AndrewJ-25/Digisax/CAD/3D_printing/step/key_low_bflat.step

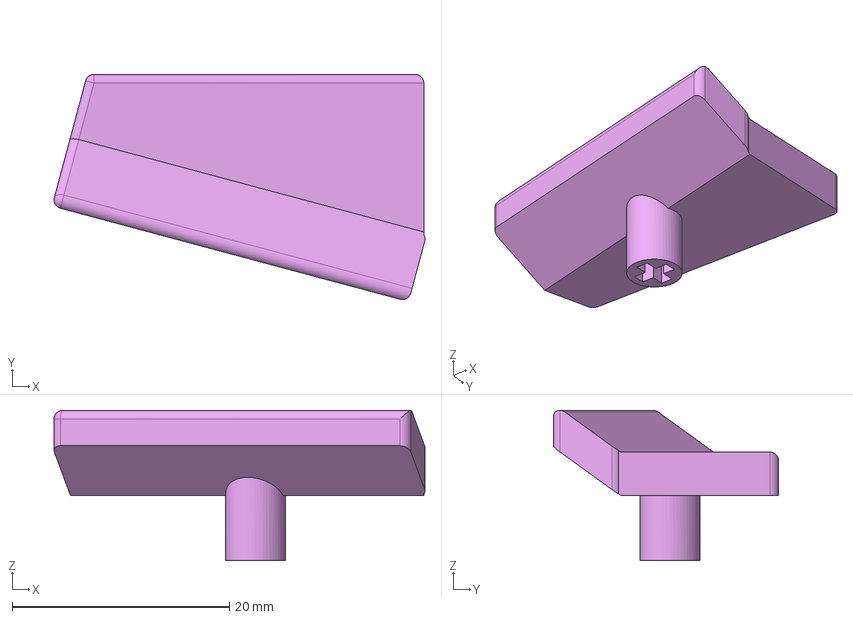
[picture p23: CAD file, 2026-06-19]
CAD/3D_printing/step/key_low_bflat.step
34.2 x 20.7 x 13.9 mm
