AndrewJ-25/Digisax/CAD/3D_printing/step/key_gsharp.step

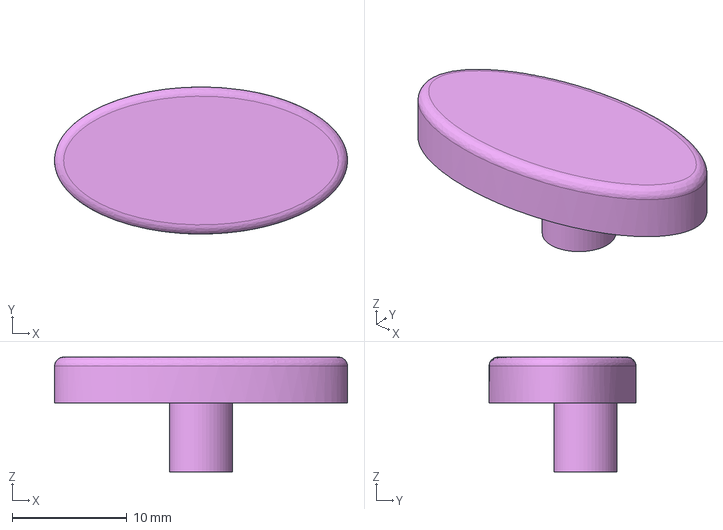
[picture p24: CAD file, 2026-06-19]
CAD/3D_printing/step/key_gsharp.step
25.5 x 12.8 x 10.0 mm
