AndrewJ-25/Digisax/CAD/3D_printing/step/key_round.step

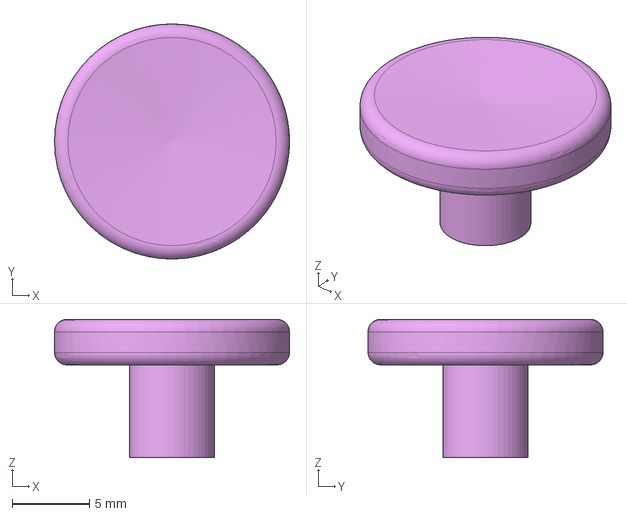
[picture p25: CAD file, 2026-06-19]
CAD/3D_printing/step/key_round.step
15.2 x 15.2 x 8.93 mm
